analoghifi/Thel-Phono-Preamps/docs/german uncorrected/THD.jpg

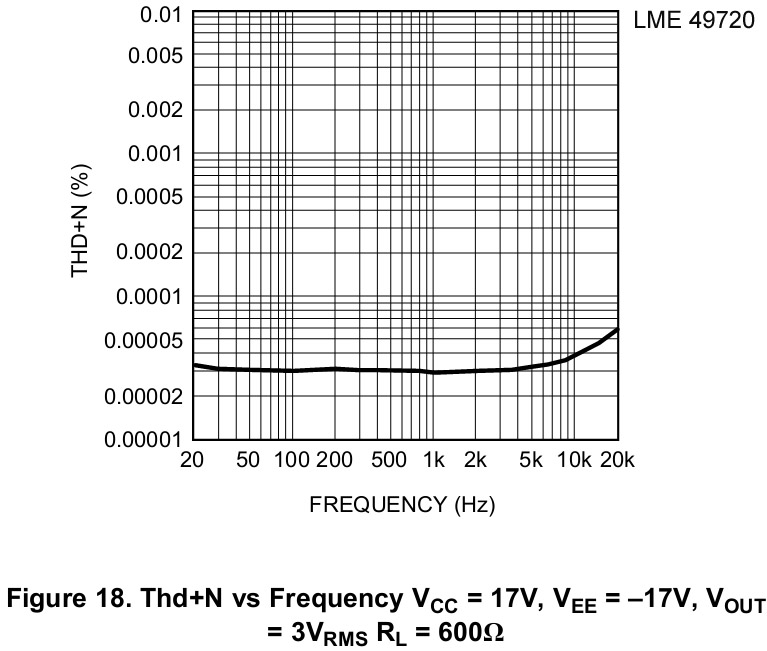
docs/german uncorrected/THD.jpg
