analoghifi/Thel-Phono-Preamps/hardware/sound of silence/KiCad/original/Sound_of_Silence_original_1Layer_THT__bottom.png

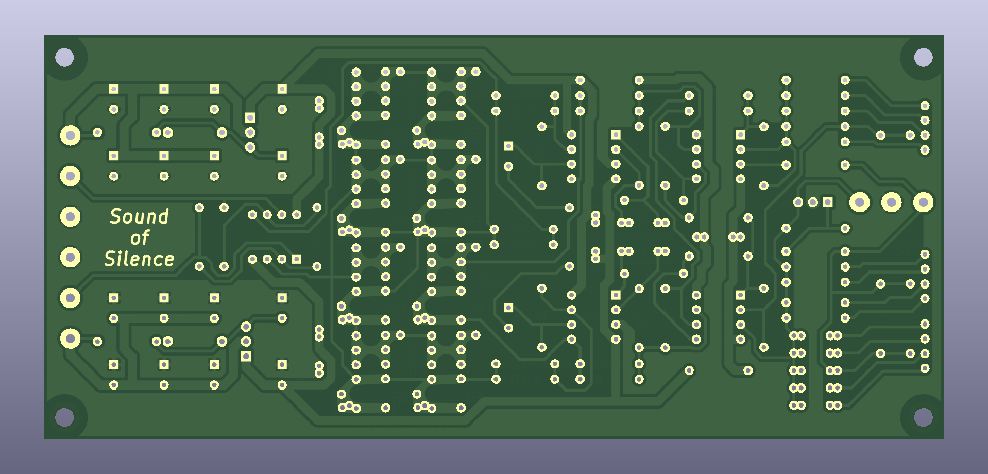
hardware/sound of silence/KiCad/original/Sound_of_Silence_original_1Layer_THT__bottom.png
