analoghifi/Thel-Phono-Preamps/hardware/sound of silence/SoS-1.jpg

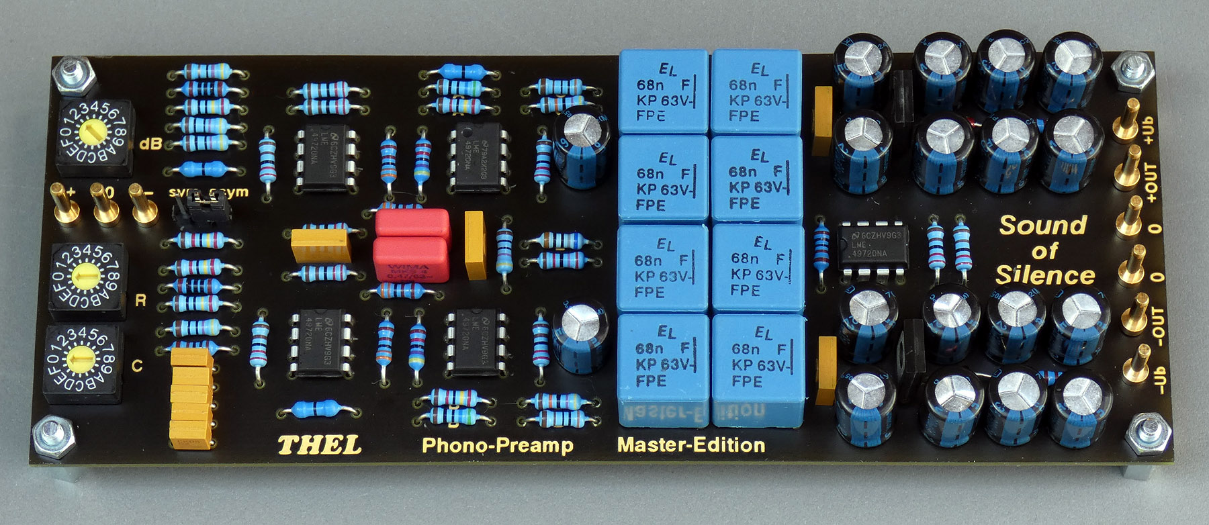
hardware/sound of silence/SoS-1.jpg
