analoghifi/Thel-Phono-Preamps/hardware/sound of silence/SoS-4.jpg

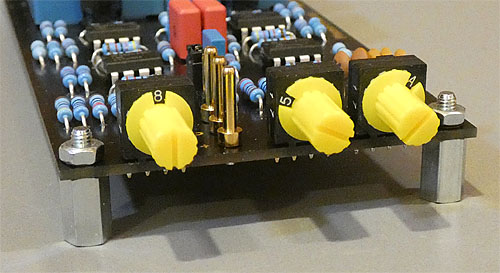
hardware/sound of silence/SoS-4.jpg
