analoghifi/Thel-Phono-Preamps/hardware/sound of silence/SoS-5.jpg

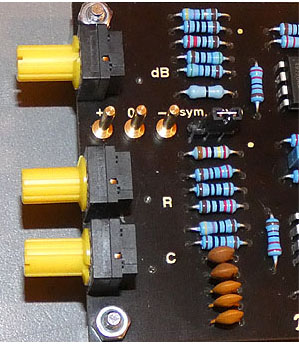
hardware/sound of silence/SoS-5.jpg
