analoghifi/Thel-Phono-Preamps/pics/Majestic__1998.jpg

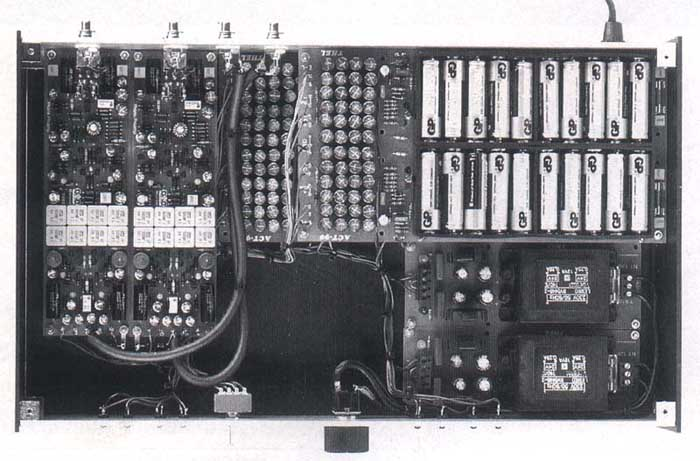
pics/Majestic__1998.jpg
