analoghifi/Thel-Phono-Preamps/pics/Phono-HQ_2018.jpg

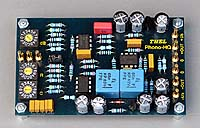
pics/Phono-HQ_2018.jpg
