analoghifi/Thel-Phono-Preamps/pics/Phono-HQX_2018.jpg

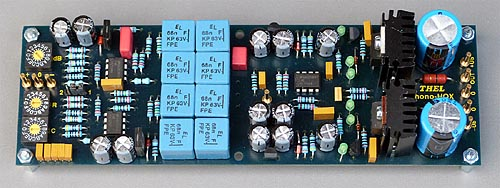
pics/Phono-HQX_2018.jpg
