analoghifi/Thel-Phono-Preamps/pics/Phono-M_2016.jpg

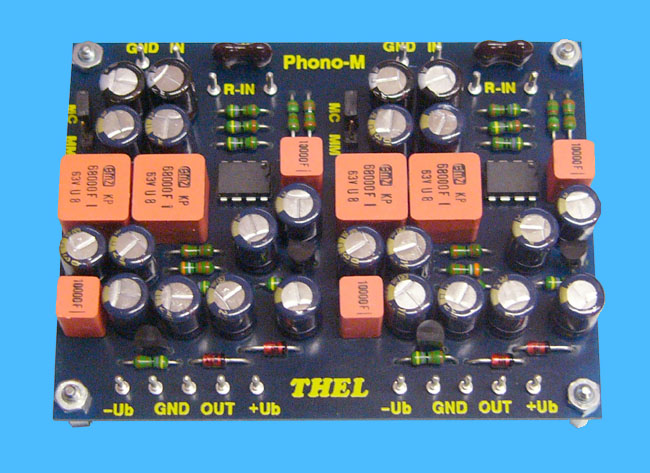
pics/Phono-M_2016.jpg
