analoghifi/Thel-Phono-Preamps/pics/Phono-X_2016.jpg

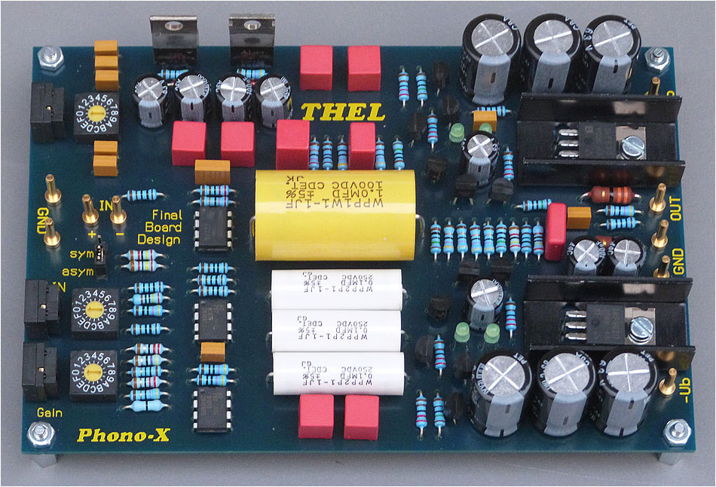
pics/Phono-X_2016.jpg
