analoghifi/Thel-Phono-Preamps/pics/Phono-X__2007.jpg

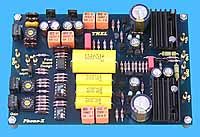
pics/Phono-X__2007.jpg
