analoghifi/Thel-Phono-Preamps/pics/Thel_Phono-M.jpg

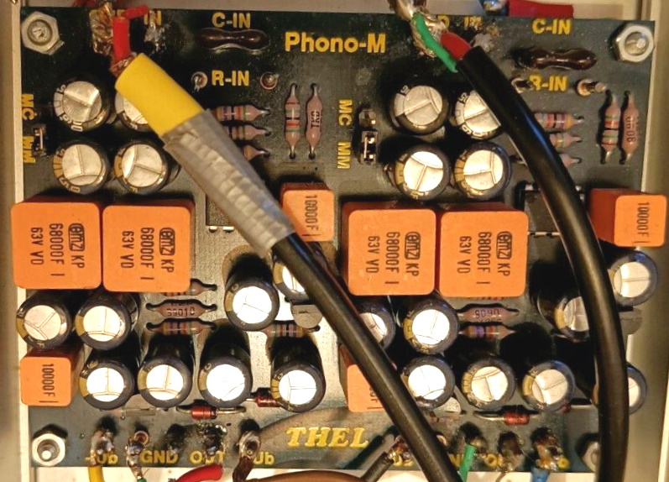
pics/Thel_Phono-M.jpg
