analoghifi/Thel-Phono-Preamps/pics/Thel_Phono_X_01.jpg

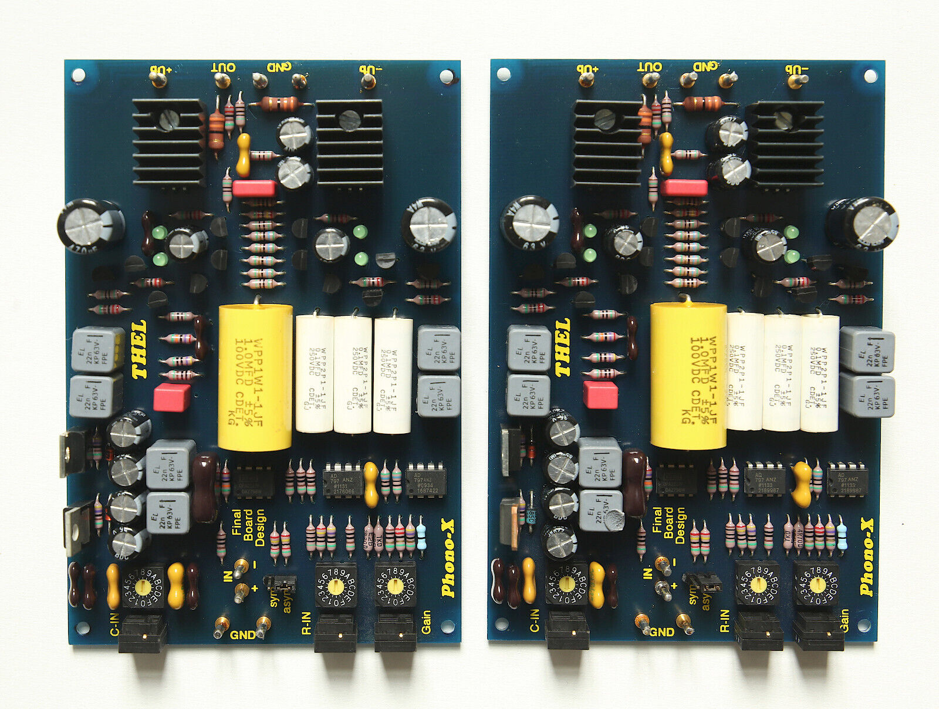
pics/Thel_Phono_X_01.jpg
