analoghifi/Thel-Phono-Preamps/pics/Thel_Phono_X_02.jpg

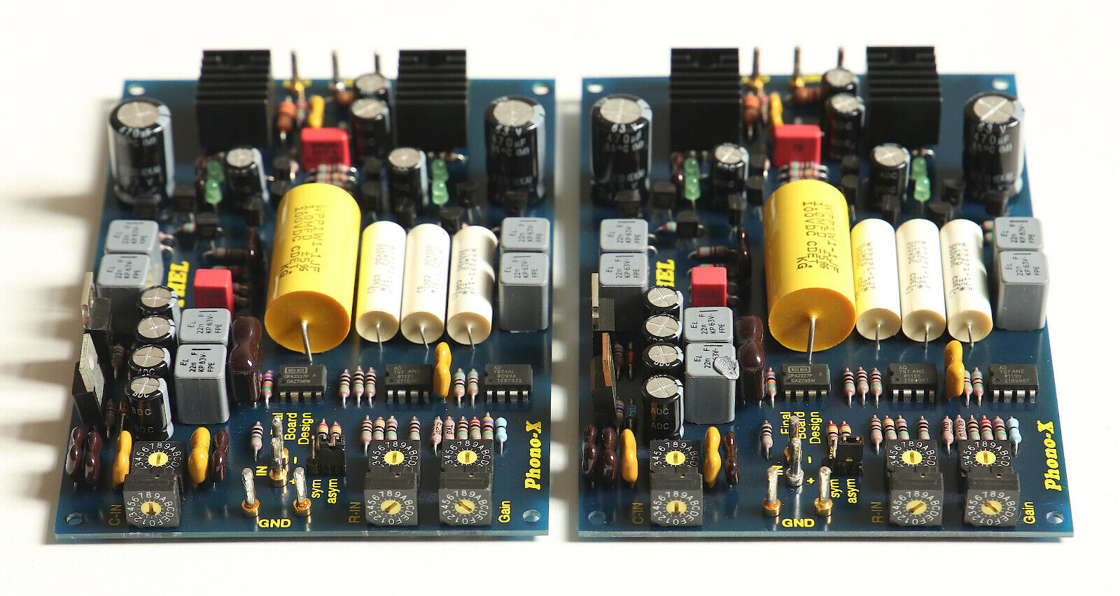
pics/Thel_Phono_X_02.jpg
