analoghifi/Thel-Phono-Preamps/pics/Thel_Phono_X_03.jpg

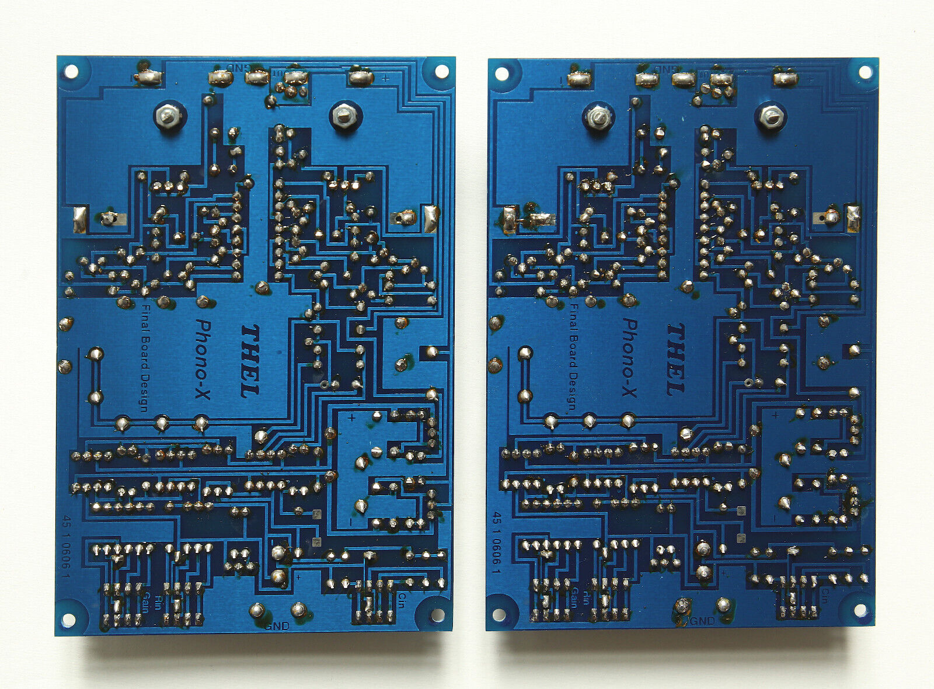
pics/Thel_Phono_X_03.jpg
