analoghifi/Thel-Phono-Preamps/pics/Thel_Phono_X_04.jpg

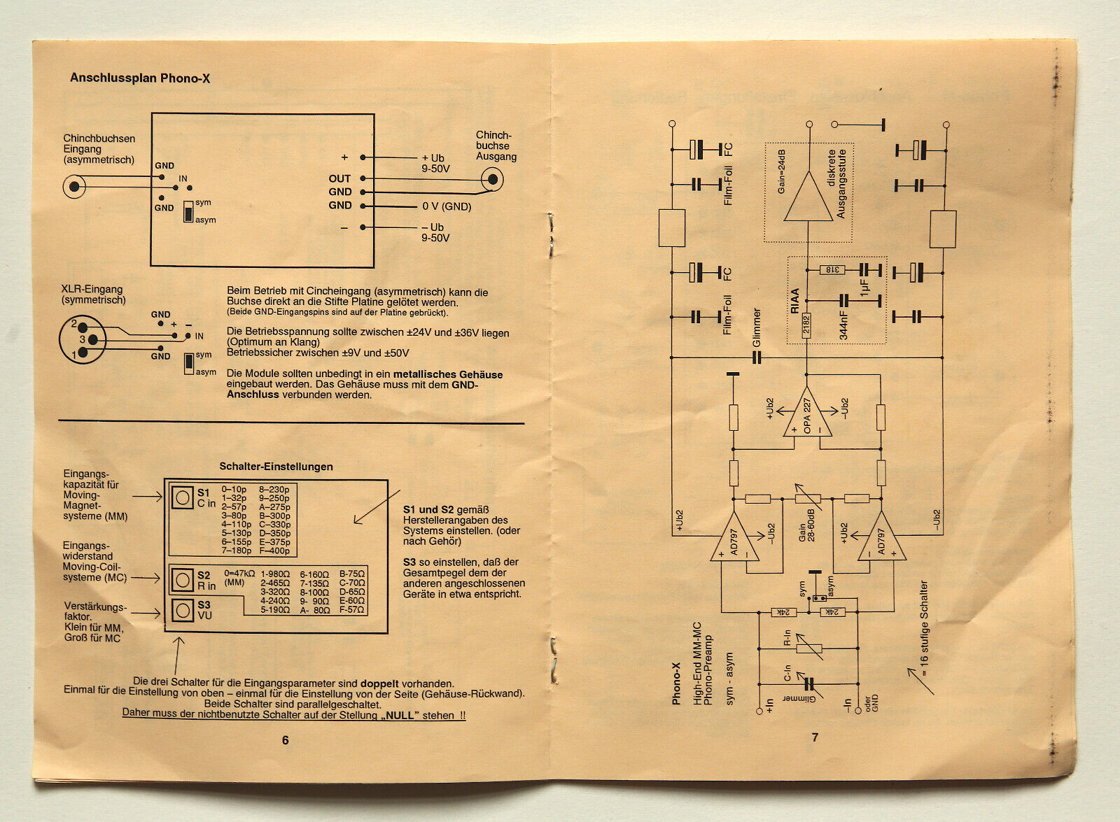
pics/Thel_Phono_X_04.jpg
