analoghifi/Thel-Phono-Preamps/pics/vp2000_2002_2.jpg

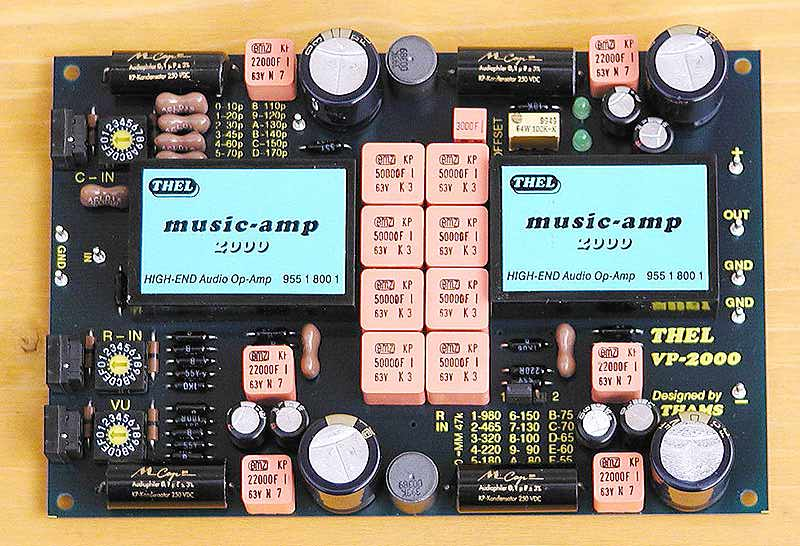
pics/vp2000_2002_2.jpg
