analoghifi/Thel-Phono-Preamps/pics/VP2000__2002.jpg

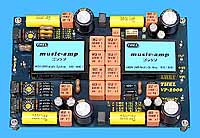
pics/VP2000__2002.jpg
