analoghifi/Thel-Phono-Preamps/pics/VX-5021P__1996.jpg

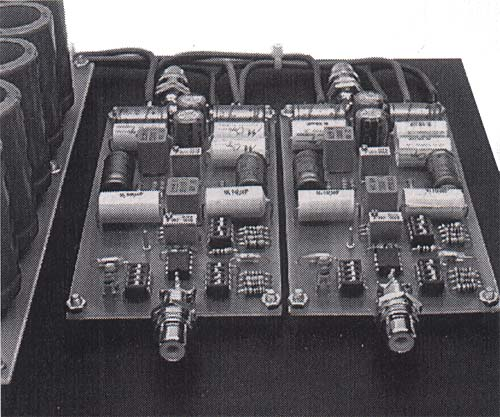
pics/VX-5021P__1996.jpg
