analoghifi/Thel-Phono-Preamps/hardware/sound of silence/component_placement_SoS.png

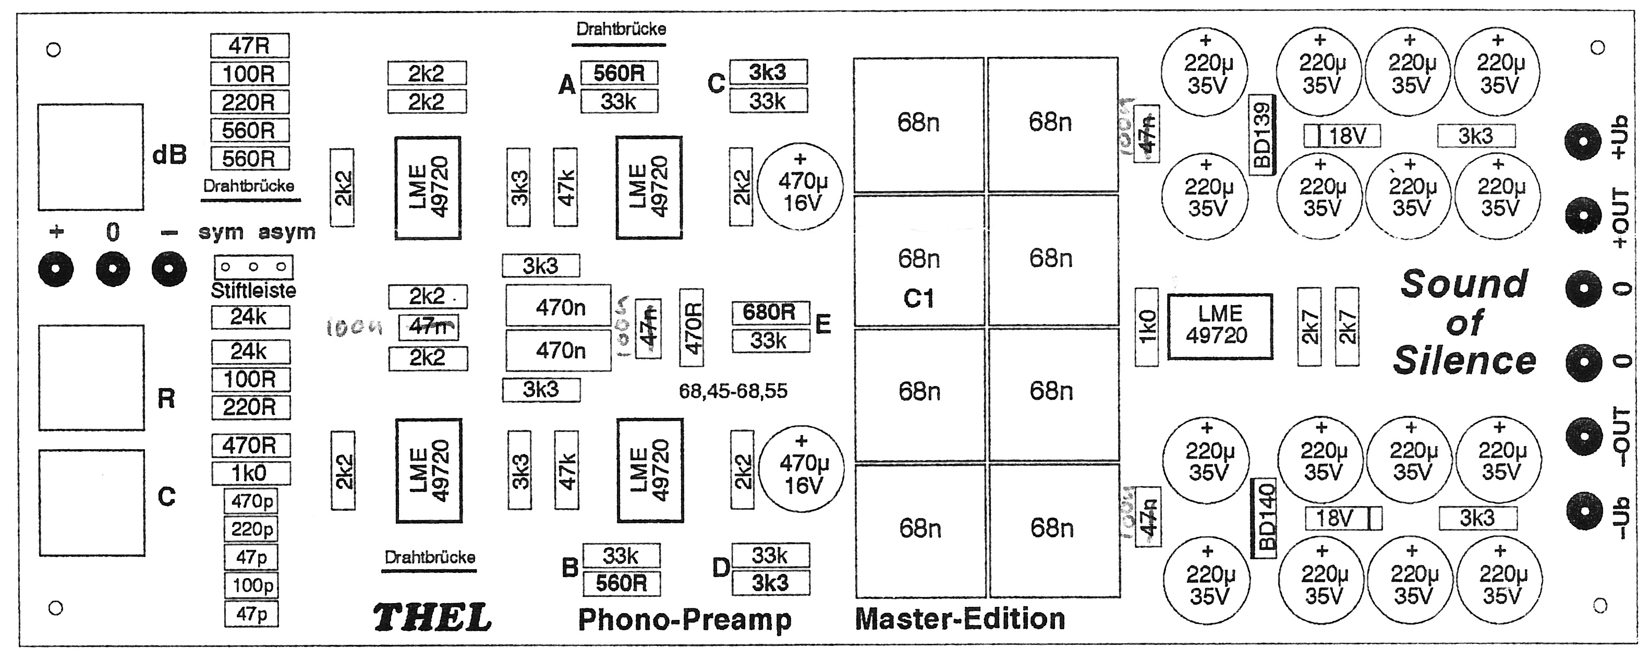
hardware/sound of silence/component_placement_SoS.png
