analoghifi/Thel-Phono-Preamps/hardware/sound of silence/KiCad/WIMA-Edition/Sound_of_Silence_WIMA_FKP_1Layer_THT__top_assembled.png

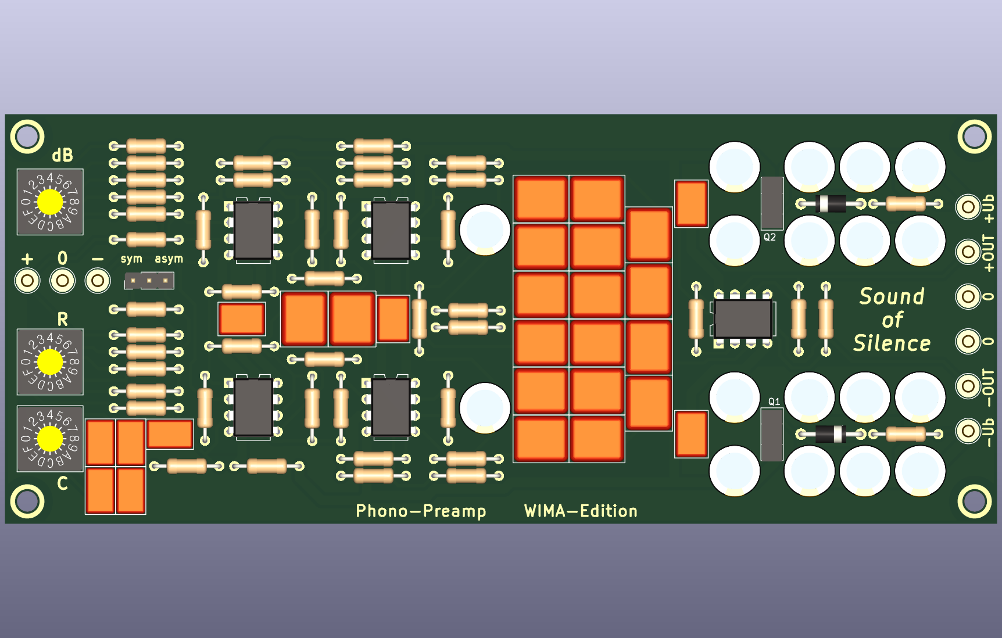
hardware/sound of silence/KiCad/WIMA-Edition/Sound_of_Silence_WIMA_FKP_1Layer_THT__top_assembled.png
